AndreasNielsen4000/Group-7-IoT-Project/NRF_COM_HUB/WifiCredentials.h

class WifiCredentials {
    public:
        const static char *SSID;
        const static char *PASSWORD;
};

/* Create a WifiCredentials.cpp with the following content:
#include "WifiCredentials.h"
const char *WifiCredentials::SSID = "SSID Name";
const char *WifiCredentials::PASSWORD = "Password";
*/
